ksjoberg/Teensy4Modbus/include/lwipopts.h

/*
 * Copyright (c) 2001-2003 Swedish Institute of Computer Science.
 * All rights reserved. 
 * 
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
 * This file is part of the lwIP TCP/IP stack.
 * 
 * Author: Simon Goldschmidt
 *
 */
#ifndef __LWIPOPTS_H__
#define __LWIPOPTS_H__

/* Prevent having to link sys_arch.c (we don't test the API layers in unit tests) */
#define NO_SYS                          1
//#define SYS_LIGHTWEIGHT_PROT            0
#define MEM_ALIGNMENT                   4
#define LWIP_RAW                        0
#define LWIP_NETCONN                    0
#define LWIP_SOCKET                     0
#define LWIP_DHCP                       0
#define LWIP_ICMP                       1
#define LWIP_UDP                        1
#define LWIP_TCP                        1
#define ETH_PAD_SIZE                    0
#define LWIP_IP_ACCEPT_UDP_PORT(p)      ((p) == PP_NTOHS(67))

#define TCP_MSS                         (1500 /*mtu*/ - 20 /*iphdr*/ - 20 /*tcphhr*/)
#define TCP_SND_BUF                     (2 * TCP_MSS)

#define ETHARP_SUPPORT_STATIC_ENTRIES   1

#define LWIP_HTTPD_CGI                  0
#define LWIP_HTTPD_SSI                  0
#define LWIP_HTTPD_SSI_INCLUDE_TAG      0

#define LWIP_SINGLE_NETIF               1

#define MEM_LIBC_MALLOC                 1
#endif /* __LWIPOPTS_H__ */
